UAA-F14/ComplexCalc-HW/code/06ComplexCalcDasProject/Core/Inc/testimg.h

#ifndef TESTIMG_H
#define TESTIMG_H
#define IE8BITPK_HEIGHT 30
#define IE8BITPK_WIDTH 30

// array size is 1800
static const uint16_t IE8BITPK[]  = {
  0xbbfe, 0xbbfe, 0xbbfe, 0xbbfe, 0xbbfe, 0xbbfe, 0xbbfe, 0xbbfe, 0xbbfe, 0xbbfe, 0xbbfe, 0xbbfe, 0xbbfe, 0xbbfe, 0xbbfe, 0xbbfe, 0xbbfe, 0xbbfe, 0xbbfe, 0xbbfe, 0xbbfe, 0xbbfe, 0xbbfe, 0xbbfe, 0xbbfe, 0xbbfe, 0xbbfe, 0xbbfe, 0xbbfe, 0xbbfe, 
  0xbbfe, 0xbbfe, 0xbbfe, 0xbbfe, 0xbbfe, 0xbbfe, 0xbbfe, 0xbbfe, 0xbbfe, 0xbbfe, 0xbbfe, 0xbbfe, 0xbbfe, 0xb9fe, 0xb5fe, 0xb9fe, 0xbbfe, 0xbbfe, 0xbbfe, 0xbbfe, 0xbbfe, 0xbbfe, 0xbbfe, 0xbbfe, 0xbbfe, 0xbbfe, 0xbbfe, 0xbbfe, 0xbbfe, 0xbbfe, 
  0xbbfe, 0xbbfe, 0xbbfe, 0xbbfe, 0xbbfe, 0xbbfe, 0xbbfe, 0xbbfe, 0xbbfe, 0xbbfe, 0xbbfe, 0xbbfe, 0xbbfe, 0xb5fe, 0xc5fd, 0x69fe, 0xb9fe, 0xbbfe, 0xbbfe, 0xbbfe, 0xbbfe, 0xbbfe, 0xbbfe, 0xbbfe, 0xbbfe, 0xbbfe, 0xbbfe, 0xbbfe, 0xbbfe, 0xbbfe, 
  0xbbfe, 0xbbfe, 0xbbfe, 0xbbfe, 0xbbfe, 0xbbfe, 0xbbfe, 0xbbfe, 0xbbfe, 0xbbfe, 0xbbfe, 0xbbfe, 0xbbfe, 0xb1fe, 0x81fd, 0xc3fd, 0x6ffe, 0xbbfe, 0xbbfe, 0xbbfe, 0xbbfe, 0xbbfe, 0xbbfe, 0xbbfe, 0xbbfe, 0xbbfe, 0xbbfe, 0xbbfe, 0xbbfe, 0xbbfe, 
  0xbbfe, 0xbbfe, 0xbbfe, 0xbbfe, 0xbbfe, 0xbbfe, 0xbbfe, 0xbbfe, 0xbbfe, 0xbbfe, 0xbbfe, 0xbbfe, 0xb9fe, 0x1bfe, 0x81fd, 0x81fd, 0xcdfd, 0xb7fe, 0xbbfe, 0xbbfe, 0xbbfe, 0xbbfe, 0xbbfe, 0xbbfe, 0xbbfe, 0xbbfe, 0xbbfe, 0xbbfe, 0xbbfe, 0xbbfe, 
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
  0x0921, 0x0921, 0x0921, 0x0921, 0x0921, 0x0921, 0x0921, 0x0921, 0x0921, 0x0921, 0x0921, 0x0921, 0x0921, 0x0921, 0x0921, 0x0921, 0x0921, 0x0921, 0x0921, 0x0921, 0x0921, 0x0921, 0x0921, 0x0921, 0x0921, 0x0921, 0x0921, 0x0921, 0x0921, 0x0921
};

#endif
